sgibeault/CSULA_RoboSub2019_Club/Stabilization_and_Depth_Control/Basic_Barometer_Test_and_Wiring/Basic_Barometer_Test_and_Wiring.ino

/*
 * On arduino, the wiring for the level shifter is as follows:
 * On the 5V side, from top to bottom the order is 5V, SCL, SDA, GND
 * (these connect directly to the arduino) 
 * On the 3V side from top to bottom the order is red, green, white, black 
 * (the barometer is connected directly to this side)
 */

#include <Wire.h>
#include "MS5837.h"

MS5837 sensor;

void setup() {
  
  Serial.begin(9600);
  
  Serial.println("Starting");
  
  Wire.begin();

  sensor.init();
  
  sensor.setFluidDensity(997); // kg/m^3 (997 freshwater, 1029 for seawater)
}

void loop() {

  sensor.read();

  Serial.print("Pressure: "); 
  Serial.print(sensor.pressure()); 
  Serial.println(" mbar");
  
  /*Serial.print("Temperature: "); 
  Serial.print(sensor.temperature()); 
  Serial.println(" deg C");
  
  Serial.print("Depth: "); 
  Serial.print(sensor.depth()); 
  Serial.println(" m");
  
  Serial.print("Altitude: "); 
  Serial.print(sensor.altitude()); 
  Serial.println(" m above mean sea level");

*/

  delay(100);
}
